profdc9/ISACard/ISA2Arduino/w5500.cpp

/*
   Copyright (c) 2013, WIZnet Co., Ltd.
   Copyright (c) 2016, Nicholas Humfrey
   All rights reserved.

   Redistribution and use in source and binary forms, with or without
   modification, are permitted provided that the following conditions
   are met:
   1. Redistributions of source code must retain the above copyright
      notice, this list of conditions and the following disclaimer.
   2. Redistributions in binary form must reproduce the above copyright
      notice, this list of conditions and the following disclaimer in the
      documentation and/or other materials provided with the distribution.
   3. Neither the name of the copyright holder nor the names of its
      contributors may be used to endorse or promote products derived
      from this software without specific prior written permission.

   THIS SOFTWARE IS PROVIDED BY THE COPYRIGHT HOLDERS AND CONTRIBUTORS
   ``AS IS'' AND ANY EXPRESS OR IMPLIED WARRANTIES, INCLUDING, BUT NOT
   LIMITED TO, THE IMPLIED WARRANTIES OF MERCHANTABILITY AND FITNESS
   FOR A PARTICULAR PURPOSE ARE DISCLAIMED.  IN NO EVENT SHALL THE
   COPYRIGHT HOLDER OR CONTRIBUTORS BE LIABLE FOR ANY DIRECT, INDIRECT,
   INCIDENTAL, SPECIAL, EXEMPLARY, OR CONSEQUENTIAL DAMAGES
   (INCLUDING, BUT NOT LIMITED TO, PROCUREMENT OF SUBSTITUTE GOODS OR
   SERVICES; LOSS OF USE, DATA, OR PROFITS; OR BUSINESS INTERRUPTION)
   HOWEVER CAUSED AND ON ANY THEORY OF LIABILITY, WHETHER IN CONTRACT,
   STRICT LIABILITY, OR TORT (INCLUDING NEGLIGENCE OR OTHERWISE)
   ARISING IN ANY WAY OUT OF THE USE OF THIS SOFTWARE, EVEN IF ADVISED
   OF THE POSSIBILITY OF SUCH DAMAGE.

*/

/* Changes for outputting to 82C55 added by Daniel Marks, marked by
   PINDEFS */

#include <Arduino.h>

#include "w5500.h"

#ifdef PINDEFS
#include "pindefs.h"
#else
#include <SPI.h>
#endif

#ifdef BITBANG_WRITE_SERIAL
extern "C" {
extern void write_dbg_string(const char *c);
extern void write_dbg_number(uint16_t n);
};
#else
#define write_dbg_string(x) {}
#define write_dbg_number(x) {}
#endif

uint8_t Wiznet5500::wizchip_read(uint8_t block, uint16_t address)
{
  uint8_t ret;

  wizchip_cs_select();

  block |= AccessModeRead;

  wizchip_spi_write_byte((address & 0xFF00) >> 8);
  wizchip_spi_write_byte((address & 0x00FF) >> 0);
  wizchip_spi_write_byte(block);

  ret = wizchip_spi_read_byte();

  wizchip_cs_deselect();
  return ret;
}

uint16_t Wiznet5500::wizchip_read_word(uint8_t block, uint16_t address)
{
  return ((uint16_t)wizchip_read(block, address) << 8) + wizchip_read(block, address + 1);
}

void Wiznet5500::wizchip_read_buf(uint8_t block, uint16_t address, uint8_t* pBuf, uint16_t len)
{
  uint16_t i;

  wizchip_cs_select();

  block |= AccessModeRead;

  wizchip_spi_write_byte((address & 0xFF00) >> 8);
  wizchip_spi_write_byte((address & 0x00FF) >> 0);
  wizchip_spi_write_byte(block);
#ifdef PINDEFS
  if (pBuf == NULL)
  {
    DATAPORT_MODE_TRANS();
    for (int i = 0; i < len; i++)
    {
      uint8_t bt = wizchip_spi_read_byte();
      while (READ_IBFA() != 0);
      WRITE_DATAPORT(bt);
      STB_LOW();
      STB_HIGH();
    }
    DATAPORT_MODE_RECEIVE();
  } else
#endif
  {
    for (i = 0; i < len; i++)
      pBuf[i] = wizchip_spi_read_byte();
  }

  wizchip_cs_deselect();
}

void Wiznet5500::wizchip_write(uint8_t block, uint16_t address, uint8_t wb)
{
  wizchip_cs_select();

  block |= AccessModeWrite;

  wizchip_spi_write_byte((address & 0xFF00) >> 8);
  wizchip_spi_write_byte((address & 0x00FF) >> 0);
  wizchip_spi_write_byte(block);
  wizchip_spi_write_byte(wb);

  wizchip_cs_deselect();
}

void Wiznet5500::wizchip_write_word(uint8_t block, uint16_t address, uint16_t word)
{
  wizchip_write(block, address,   (uint8_t)(word >> 8));
  wizchip_write(block, address + 1, (uint8_t) word);
}

void Wiznet5500::wizchip_write_buf(uint8_t block, uint16_t address, const uint8_t* pBuf, uint16_t len)
{
  uint16_t i;

  wizchip_cs_select();

  block |= AccessModeWrite;

  wizchip_spi_write_byte((address & 0xFF00) >> 8);
  wizchip_spi_write_byte((address & 0x00FF) >> 0);
  wizchip_spi_write_byte(block);
#ifdef PINDEFS
  if (pBuf == NULL)
  {
    for (i = 0; i < len; i++)
    {
      while (READ_OBFA() != 0);
      ACK_LOW();
      uint8_t bt = READ_DATAPORT();
      ACK_HIGH();
      wizchip_spi_write_byte(bt);
    }
  } else
#endif
  {
    for (i = 0; i < len; i++)
      wizchip_spi_write_byte(pBuf[i]);
  }

  wizchip_cs_deselect();
}

void Wiznet5500::setSn_CR(uint8_t cr) {
  // Write the command to the Command Register
  wizchip_write(BlockSelectSReg, Sn_CR, cr);

  // Now wait for the command to complete
  while ( wizchip_read(BlockSelectSReg, Sn_CR) );
}

uint16_t Wiznet5500::getSn_TX_FSR()
{
  uint16_t val = 0, val1 = 0;
  do
  {
    val1 = wizchip_read_word(BlockSelectSReg, Sn_TX_FSR);
    if (val1 != 0)
    {
      val = wizchip_read_word(BlockSelectSReg, Sn_TX_FSR);
    }
  } while (val != val1);
  return val;
}


uint16_t Wiznet5500::getSn_RX_RSR()
{
  uint16_t val = 0, val1 = 0;
  do
  {
    val1 = wizchip_read_word(BlockSelectSReg, Sn_RX_RSR);
    if (val1 != 0)
    {
      val = wizchip_read_word(BlockSelectSReg, Sn_RX_RSR);
    }
  } while (val != val1);
  return val;
}

void Wiznet5500::wizchip_send_data(const uint8_t *wizdata, uint16_t len)
{
  uint16_t ptr = 0;

  if (len == 0) return;
  ptr = getSn_TX_WR();
  wizchip_write_buf(BlockSelectTxBuf, ptr, wizdata, len);

  ptr += len;

  setSn_TX_WR(ptr);
}

void Wiznet5500::wizchip_recv_data(uint8_t *wizdata, uint16_t len)
{
  uint16_t ptr;

  if (len == 0) return;
  ptr = getSn_RX_RD();
  wizchip_read_buf(BlockSelectRxBuf, ptr, wizdata, len);
  ptr += len;

  setSn_RX_RD(ptr);
}

void Wiznet5500::wizchip_recv_ignore(uint16_t len)
{
  uint16_t ptr;

  ptr = getSn_RX_RD();
  ptr += len;
  setSn_RX_RD(ptr);
}

void Wiznet5500::wizchip_sw_reset()
{
  setMR(MR_RST);
  getMR(); // for delay

  setSHAR(_mac_address);
}

int8_t Wiznet5500::wizphy_getphylink()
{
  int8_t tmp;
  if (getPHYCFGR() & PHYCFGR_LNK_ON)
    tmp = PHY_LINK_ON;
  else
    tmp = PHY_LINK_OFF;
  return tmp;
}

int8_t Wiznet5500::wizphy_getphypmode()
{
  int8_t tmp = 0;
  if (getPHYCFGR() & PHYCFGR_OPMDC_PDOWN)
    tmp = PHY_POWER_DOWN;
  else
    tmp = PHY_POWER_NORM;
  return tmp;
}

void Wiznet5500::wizphy_reset()
{
  uint8_t tmp = getPHYCFGR();
  tmp &= PHYCFGR_RST;
  setPHYCFGR(tmp);
  tmp = getPHYCFGR();
  tmp |= ~PHYCFGR_RST;
  setPHYCFGR(tmp);
}

int8_t Wiznet5500::wizphy_setphypmode(uint8_t pmode)
{
  uint8_t tmp = 0;
  tmp = getPHYCFGR();
  if ((tmp & PHYCFGR_OPMD) == 0) return -1;
  tmp &= ~PHYCFGR_OPMDC_ALLA;
  if ( pmode == PHY_POWER_DOWN)
    tmp |= PHYCFGR_OPMDC_PDOWN;
  else
    tmp |= PHYCFGR_OPMDC_ALLA;
  setPHYCFGR(tmp);
  wizphy_reset();
  tmp = getPHYCFGR();
  if ( pmode == PHY_POWER_DOWN)
  {
    if (tmp & PHYCFGR_OPMDC_PDOWN) return 0;
  }
  else
  {
    if (tmp & PHYCFGR_OPMDC_ALLA) return 0;
  }
  return -1;
}


Wiznet5500::Wiznet5500(int8_t cs)
{
  _cs = cs;
}

boolean Wiznet5500::begin(const uint8_t *mac_address, bool spiinit)
{
  memcpy(_mac_address, mac_address, 6);

  if (spiinit)
  {
#ifdef PINDEFS
    cli();
    MCUCR &= ~0x10;
    PORTB = 0x07;
    DDRB = 0x2F;
    PORTB = 0x3F;
    SPCR = _BV(SPE) | _BV(MSTR);
    SPSR = _BV(SPI2X);
    sei();
#else
    pinMode(_cs, OUTPUT);
    wizchip_cs_deselect();
    SPI.begin();
    SPI.setClockDivider(SPI_CLOCK_DIV4); // 4 MHz?
    SPI.setBitOrder(MSBFIRST);
    SPI.setDataMode(SPI_MODE0);
#endif
  }

  wizchip_sw_reset();

  // Use the full 16Kb of RAM for Socket 0
  setSn_RXBUF_SIZE(16);
  setSn_TXBUF_SIZE(16);

  // Set our local MAC address
  setSHAR(_mac_address);

  // Open Socket 0 in MACRaw mode
  setSn_MR(Sn_MR_MACRAW);
  setSn_CR(Sn_CR_OPEN);
  if (getSn_SR() != SOCK_MACRAW) {
    // Failed to put socket 0 into MACRaw mode
    return false;
  }
  setSn_IR(0xFF);
  setSn_IMR(Sn_IR_RECV);
  setSIMR(0x01);
  setSIR(0x00);

  // Success
  return true;
}

void Wiznet5500::end()
{

  setSn_CR(Sn_CR_CLOSE);

  setSIMR(0x00);
  setSn_IMR(0x00);
  setSIR(0xFF);
  // clear all interrupt of the socket
  setSn_IR(0xFF);

  // Wait for socket to change to closed
  while (getSn_SR() != SOCK_CLOSED);
}

static void write_length(uint16_t data_len)
{
  DATAPORT_MODE_TRANS();
  while (READ_IBFA() != 0);
  WRITE_DATAPORT(data_len & 0xFF);
  STB_LOW();
  STB_HIGH();
  while (READ_IBFA() != 0);
  WRITE_DATAPORT(data_len >> 8);
  STB_LOW();
  STB_HIGH();
  DATAPORT_MODE_RECEIVE();
}

uint16_t Wiznet5500::remainderFrame()
{
  uint16_t len = getSn_RX_RSR();
  return len;
}

uint16_t Wiznet5500::discardFrame()
{
  uint16_t len = getSn_RX_RSR();

  if (len > 0)
  {
    uint8_t head[2];
    uint16_t data_len = 0;

    wizchip_recv_data(head, 2);
    setSn_CR(Sn_CR_RECV);

    data_len = head[0];
    data_len = (data_len << 8) + head[1];
    data_len -= 2;

    wizchip_recv_ignore(data_len);
    setSn_CR(Sn_CR_RECV);
    setSIR(0x00);
    setSn_IR(0xFF);
    return data_len;
  }
  setSIR(0x00);
  setSn_IR(0xFF);
  return 0;
}

uint16_t Wiznet5500::readFrame(uint8_t *buffer, uint16_t bufsize)
{
  uint16_t len = getSn_RX_RSR();

  if (len > 0)
  {
    uint8_t head[2];
    uint16_t data_len = 0;

    wizchip_recv_data(head, 2);
    setSn_CR(Sn_CR_RECV);

    data_len = head[0];
    data_len = (data_len << 8) + head[1];
    data_len -= 2;

    if (data_len > bufsize)
    {
      // Packet is bigger than buffer - drop the packet
#ifdef PINDEFS
      if (buffer == NULL)
        write_length(0);
#endif
      wizchip_recv_ignore(data_len);
      setSn_CR(Sn_CR_RECV);
      setSIR(0x00);
      setSn_IR(0xFF);
      return 0;
    }

#ifdef PINDEFS
    if (buffer == NULL)
      write_length(data_len);
#endif
    wizchip_recv_data(buffer, data_len);
    setSn_CR(Sn_CR_RECV);
    setSIR(0x00);
    setSn_IR(0xFF);
#if 1
    return data_len;
#else
    // Had problems with W5500 MAC address filtering (the Sn_MR_MFEN option)
    // Do it in software instead:
    if ((buffer[0] & 0x01) || memcmp(&buffer[0], _mac_address, 6) == 0)
    {
      // Addressed to an Ethernet multicast address or our unicast address
      return data_len;
    } else {
      return 0;
    }
#endif
  }
#ifdef PINDEFS
  write_length(0);
#endif
  return 0;
}

uint16_t Wiznet5500::sendFrame(const uint8_t *buf, uint16_t len)
{
  // Wait for space in the transmit buffer
  while (1)
  {
    uint16_t freesize = getSn_TX_FSR();
    if (getSn_SR() == SOCK_CLOSED) {
      return -1;
    }
    if (len <= freesize) break;
  };

  wizchip_send_data(buf, len);
  setSn_CR(Sn_CR_SEND);

  while (1)
  {
    uint8_t tmp = getSn_IR();
    if (tmp & Sn_IR_SENDOK)
    {
      setSn_IR(Sn_IR_SENDOK);
      // Packet sent ok
      break;
    }
    else if (tmp & Sn_IR_TIMEOUT)
    {
      setSn_IR(Sn_IR_TIMEOUT);
      // There was a timeout
      return -1;
    }
  }
  return len;
}
